Darkace1337/N64PowerAdapter/Images/5484.jpg

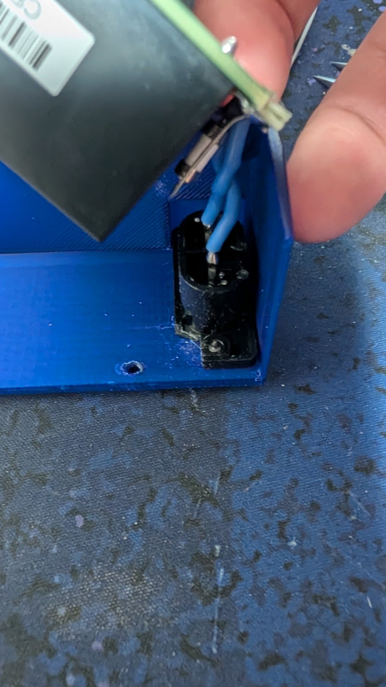
Images/5484.jpg
