Darkace1337/N64PowerAdapter/Images/5487.jpg

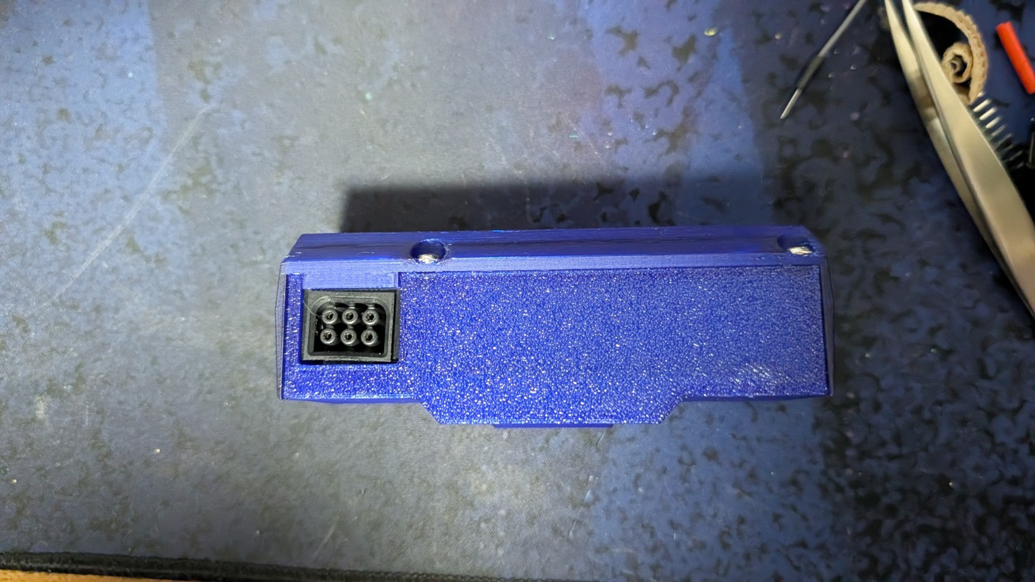
Images/5487.jpg
