Darkace1337/N64PowerAdapter/Images/5488.jpg

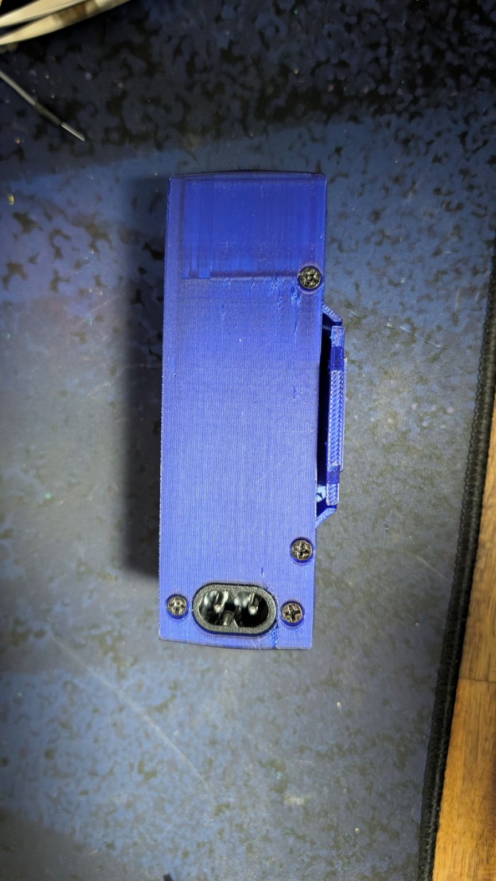
Images/5488.jpg
