Darkace1337/N64PowerAdapter/Images/5489.jpg

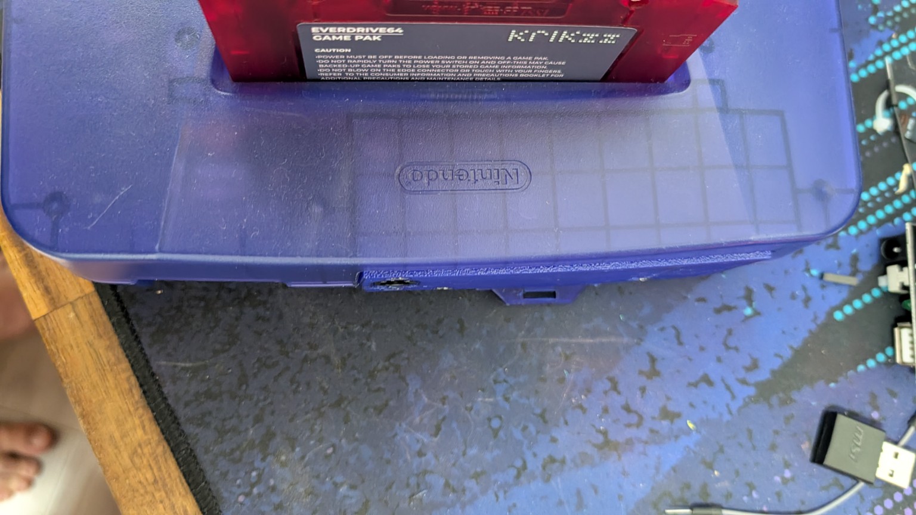
Images/5489.jpg
